Sugawarakana/Sensor-Integration/Rp2040_CAN_test/Rp2040_CAN_test.ino

// CANBED DUAL TEST EXAMPLE
// CAN 0 Send, CAN 1 Recv

#include <Wire.h>
#include <stdio.h>
#include "canbed_dual.h"

CANBedDual CAN0(0);
CANBedDual CAN1(1);


void setup()
{
    Serial.begin(115200);
    pinMode(18, OUTPUT);

    // Wire1.setSDA(6);
    // Wire1.setSCL(7);
    Wire.begin();

    CAN0.init(500000);          // CAN0 baudrate: 500kb/s
    CAN1.init(500000);          // CAN1 baudrate: 500kb/s
}

void loop()
{
    sendData();

    unsigned long id = 0;
    int ext = 0;
    int rtr = 0;
    int fd = 0;
    int len = 0;

    unsigned char dtaGet[100];

    // if(CAN1.read(&id, &ext, &rtr, &fd, &len, dtaGet))
    // {
    //     Serial.println("CAN1 GET DATA");
    //     Serial.print("id = ");
    //     Serial.println(id);
    //     Serial.print("ext = ");
    //     Serial.println(ext);
    //     Serial.print("rtr = ");
    //     Serial.println(rtr);
    //     Serial.print("fd = ");
    //     Serial.println(fd);
    //     Serial.print("len = ");
    //     Serial.println(len);

    //     for(int i=0; i<len; i++)
    //     {
    //         Serial.print(dtaGet[i]);
    //         Serial.print("\t");
    //     }
    //     Serial.println();
    // }
    len = CAN1.checkRecv();
    Serial.println(len);
    delay(1000);
}

void sendData()
{
    static unsigned int cnt = 0;
    cnt++;
    if(cnt > 99)cnt = 0;
    unsigned char str[8];
    for(int i=0; i<8; i++)str[i] = cnt;
    CAN0.send(0x01, 0, 0, 0, 8, str);
}

// ENDIF
